BX80646G3258/YADG/stl/bumper right.stl

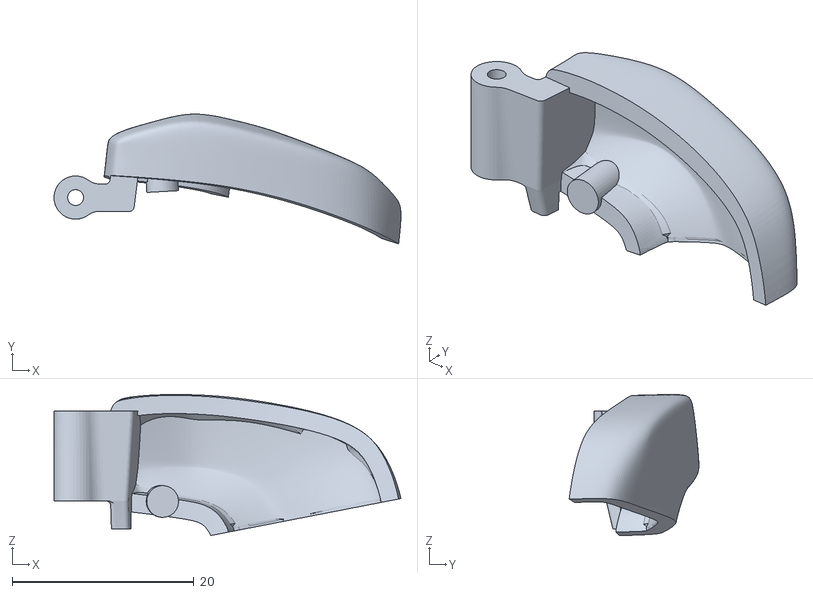
[picture p17: CAD file, 2025-11-13]
stl/bumper right.stl
38.2 x 14.3 x 15.5
