BX80646G3258/YADG/stl/dpad down button.stl

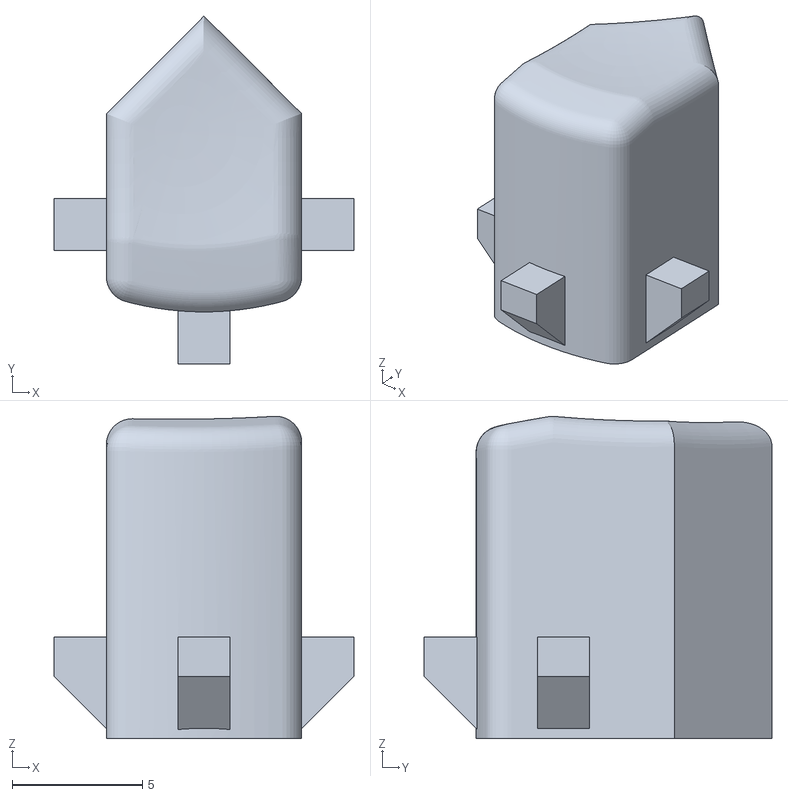
[picture p18: CAD file, 2025-11-13]
stl/dpad down button.stl
11.5 x 13.4 x 12.4
