BX80646G3258/YADG/stl/joystick.stl

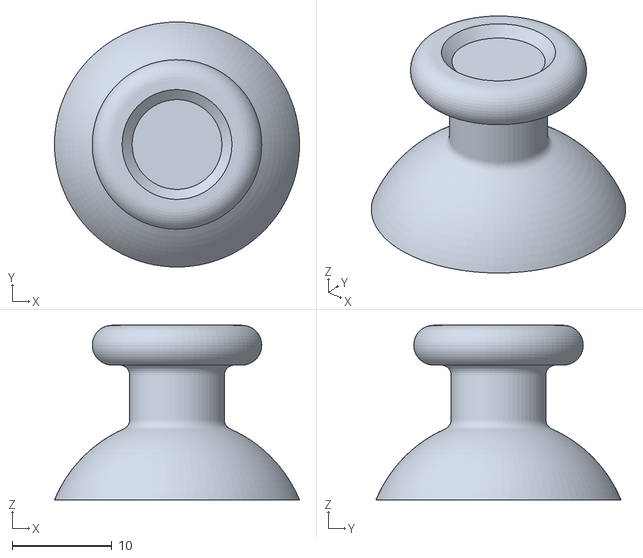
[picture p19: CAD file, 2025-11-13]
stl/joystick.stl
24.6 x 24.6 x 17.5
