BX80646G3258/YADG/stl/shell bottom.stl

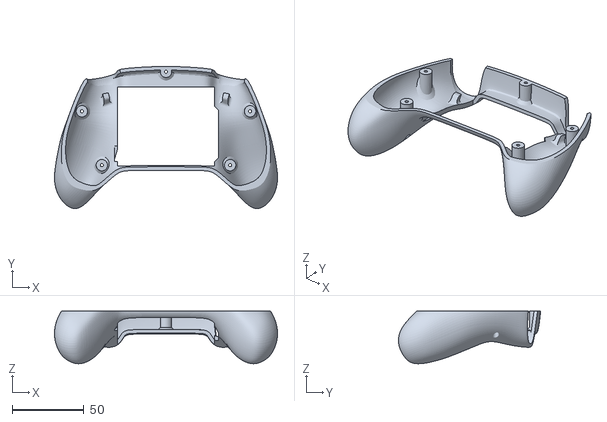
[picture p20: CAD file, 2025-11-13]
stl/shell bottom.stl
155.7 x 99.2 x 36.7
