BX80646G3258/YADG/firmware/MenuAdjustAxisMap.h

#ifndef MENUAXISMAP_H
#define MENUAXISMAP_H

#include "AxisMap.h"
#include <stdint.h>

namespace MenuAdjustAxisMap {
void adjustAxisMap(AxisMap& axisMap);
}  // namespace MenuAdjustAxisMap

#endif  // ifndef MENUAXISMAP_H
